MecaChronos9461/Project_Daedalus/STL/pt/Pecas_GCODE/F.15.stl

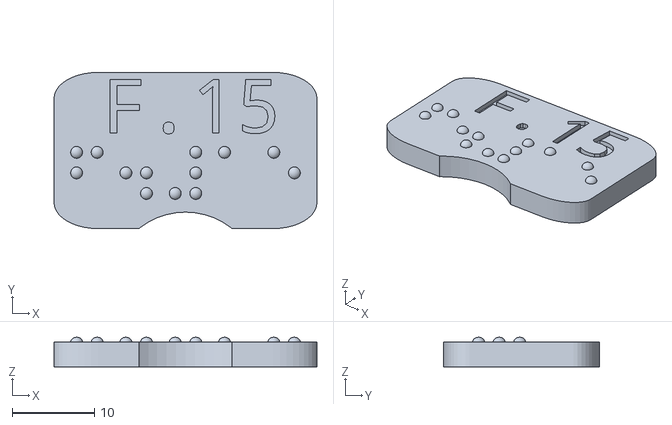
[picture p13: CAD file, 2025-11-13]
STL/pt/Pecas_GCODE/F.15.stl
32.0 x 19.0 x 3.60
