MecaChronos9461/Project_Daedalus/docs/pt/desenhos_CAD/Tabuleiro_Frente Drawing 2.pdf

R10

3

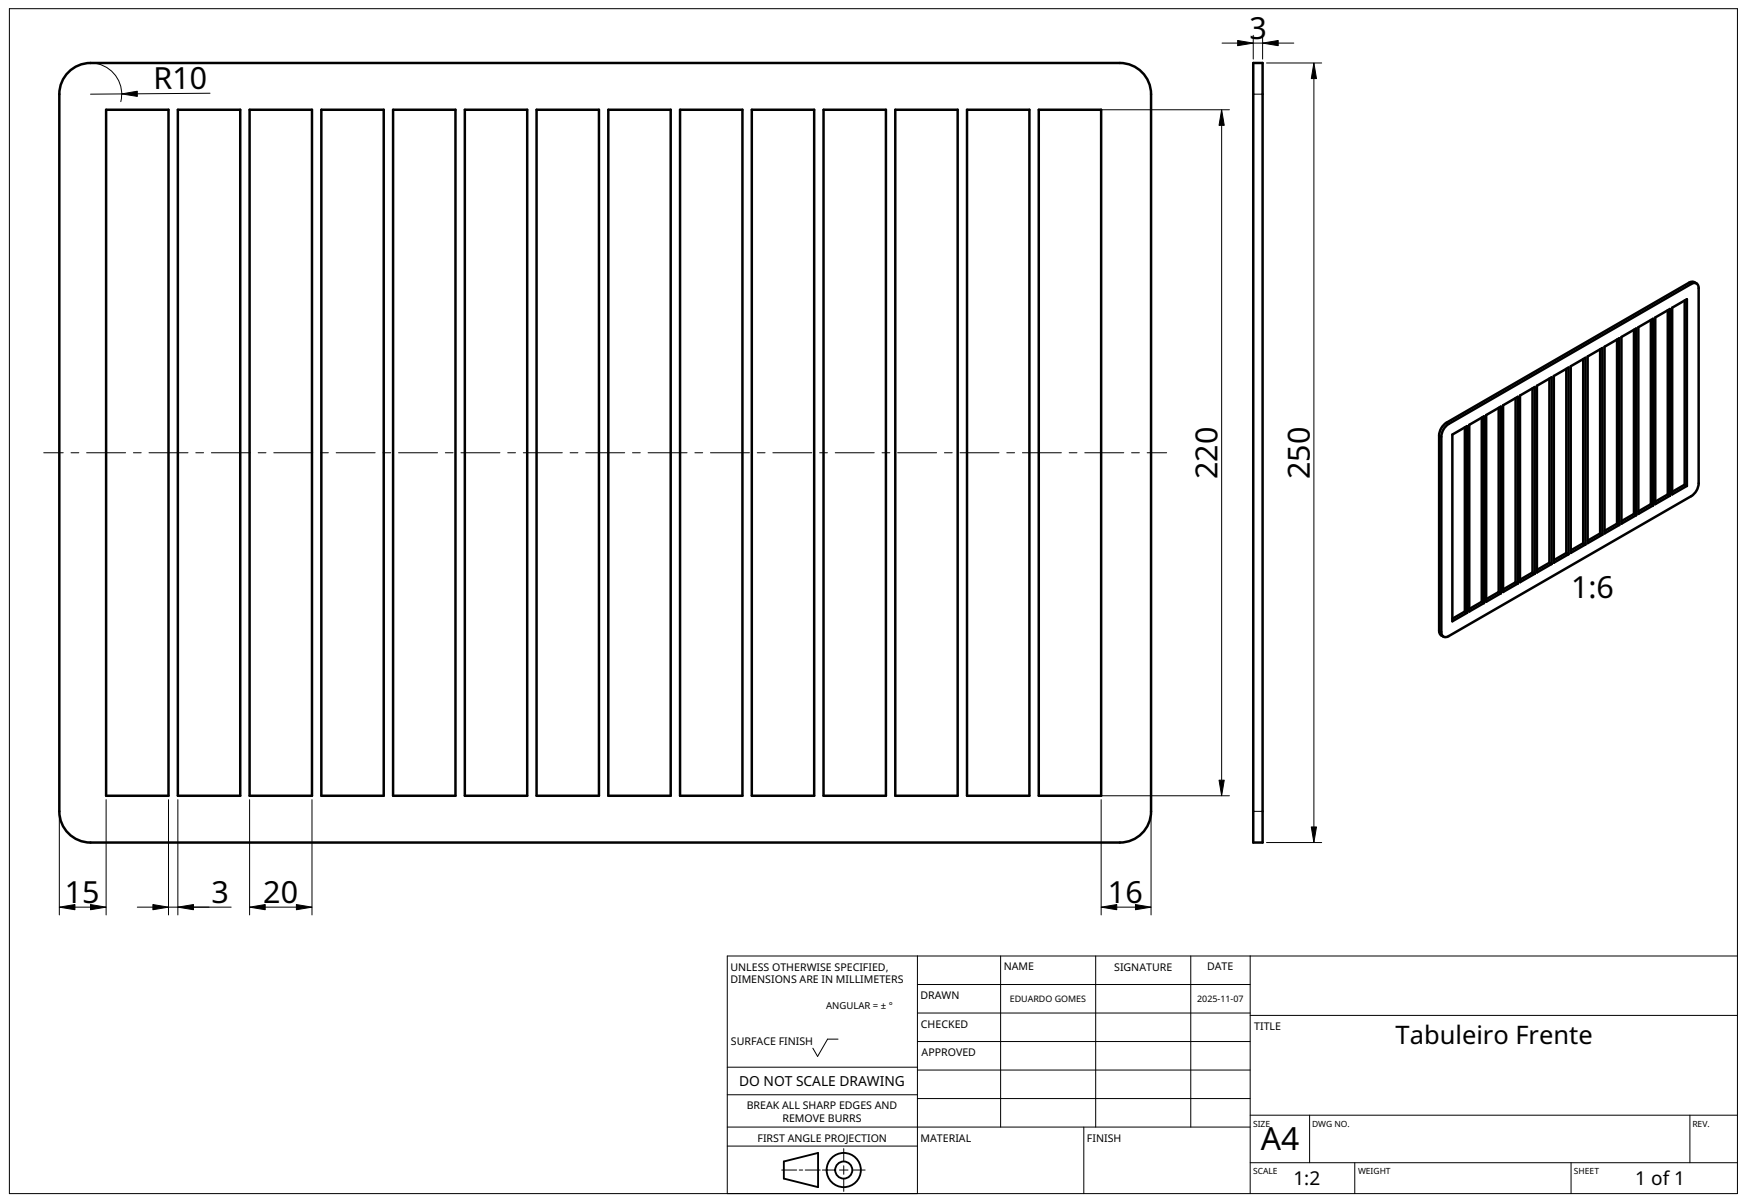
[picture p23: page 1]
MATERIAL; FINISH

UNLESS OTHERWISE SPECIFIED, DIMENSIONS ARE IN MILLIMETERS ANGULAR = ± ° SURFACE FINISH | | NAME | SIGNATURE | DATE

DRAWN | EDUARDO GOMES | | 2025-11-07

CHECKED | | | | TITLE Tabuleiro Frente

APPROVED

DO NOT SCALE DRAWING

BREAK ALL SHARP EDGES AND

REMOVE BURRS
FIRST ANGLE PROJECTION

SIZE A4 | DWG NO. | REV.

SCALE 1:2 | WEIGHT | SHEET 1 of 1
